RobertDaleSmith/mouthpad-usb/ncs/app/src/ble_nus_client.c

/*
 * Copyright (c) 2025 Robert Dale Smith
 * Copyright (c) 2025 Augmental Tech
 *
 * SPDX-License-Identifier: Apache-2.0
 */

#include "ble_nus_client.h"
#include <zephyr/kernel.h>
#include <zephyr/bluetooth/bluetooth.h>
#include <zephyr/bluetooth/conn.h>
#include <zephyr/bluetooth/uuid.h>
#include <zephyr/bluetooth/gatt.h>
#include <bluetooth/services/nus_client.h>
#include <bluetooth/services/nus.h>
#include <bluetooth/gatt_dm.h>
#include <zephyr/logging/log.h>

LOG_MODULE_REGISTER(ble_nus_client, LOG_LEVEL_INF);

/* NUS Client instance */
static struct bt_nus_client nus_client;

/* Callback functions for external modules */
static ble_nus_data_received_cb_t data_received_cb;
static ble_nus_data_sent_cb_t data_sent_cb;
static ble_nus_mtu_exchange_cb_t mtu_exchange_cb;
static ble_nus_discovery_complete_cb_t discovery_complete_cb;

/* Semaphore for NUS write operations */
K_SEM_DEFINE(nus_write_sem, 0, 1);

/* NUS Client callbacks */
static uint8_t nus_data_received(struct bt_nus_client *nus, const uint8_t *data, uint16_t len);
static void nus_data_sent(struct bt_nus_client *nus, uint8_t err, const uint8_t *const data, uint16_t len);

/* Discovery callbacks */
static void discovery_complete(struct bt_gatt_dm *dm, void *context);
static void discovery_service_not_found(struct bt_conn *conn, void *context);
static void discovery_error(struct bt_conn *conn, int err, void *context);

/* MTU exchange callback */
static void exchange_func(struct bt_conn *conn, uint8_t err, struct bt_gatt_exchange_params *params);

/* Discovery callback structure */
struct bt_gatt_dm_cb discovery_cb = {
	.completed = discovery_complete,
	.service_not_found = discovery_service_not_found,
	.error_found = discovery_error,
};

/* NUS Client callback implementations */
static uint8_t nus_data_received(struct bt_nus_client *nus, const uint8_t *data, uint16_t len)
{
	ARG_UNUSED(nus);

	// Call external data received callback if registered
	if (data_received_cb) {
		data_received_cb(data, len);
	}

	return BT_GATT_ITER_CONTINUE;
}

static void nus_data_sent(struct bt_nus_client *nus, uint8_t err, const uint8_t *const data, uint16_t len)
{
	ARG_UNUSED(nus);
	ARG_UNUSED(data);
	ARG_UNUSED(len);

	k_sem_give(&nus_write_sem);

	if (err) {
		LOG_WRN("ATT error code: 0x%02X", err);
	}

	// Call external data sent callback if registered
	if (data_sent_cb) {
		data_sent_cb(err);
	}
}

/* Discovery callback implementations */
static void discovery_complete(struct bt_gatt_dm *dm, void *context)
{
	struct bt_nus_client *nus = context;
	LOG_INF("Service discovery completed");

	bt_gatt_dm_data_print(dm);

	bt_nus_handles_assign(dm, nus);
	bt_nus_subscribe_receive(nus);

	bt_gatt_dm_data_release(dm);

	// Call external discovery complete callback if registered
	if (discovery_complete_cb) {
		discovery_complete_cb();
	}
}

static void discovery_service_not_found(struct bt_conn *conn, void *context)
{
	LOG_INF("Service not found");
}

static void discovery_error(struct bt_conn *conn, int err, void *context)
{
	LOG_WRN("Error while discovering GATT database: (%d)", err);
}

/* MTU exchange callback implementation */
static void exchange_func(struct bt_conn *conn, uint8_t err, struct bt_gatt_exchange_params *params)
{
	ARG_UNUSED(conn);
	ARG_UNUSED(params);

	if (!err) {
		uint16_t mtu = bt_gatt_get_mtu(conn);
		LOG_INF("MTU EXCHANGE SUCCESSFUL: MTU = %d bytes", mtu);

		// Call external MTU exchange callback if registered
		if (mtu_exchange_cb) {
			mtu_exchange_cb(mtu);
		}
	} else {
		LOG_ERR("MTU EXCHANGE FAILED: error = %d", err);
	}
}

/* Public API implementations */
int ble_nus_client_init(void)
{
	int err;
	struct bt_nus_client_init_param init = {
		.cb = {
			.received = nus_data_received,
			.sent = nus_data_sent,
		}
	};

	err = bt_nus_client_init(&nus_client, &init);
	if (err) {
		LOG_ERR("NUS Client initialization failed (err %d)", err);
		return err;
	}

	LOG_INF("NUS Client module initialized");
	return err;
}

int ble_nus_client_send_data(const uint8_t *data, uint16_t len)
{
	if (!data || len == 0) {
		return -EINVAL;
	}

	return bt_nus_client_send(&nus_client, data, len);
}

void ble_nus_client_discover(struct bt_conn *conn)
{
	int err;

	err = bt_gatt_dm_start(conn,
			       BT_UUID_NUS_SERVICE,
			       &discovery_cb,
			       &nus_client);
	if (err) {
		LOG_ERR("could not start the discovery procedure, error "
			"code: %d", err);
	}
}

void ble_nus_client_register_data_received_cb(ble_nus_data_received_cb_t cb)
{
	data_received_cb = cb;
}

void ble_nus_client_register_data_sent_cb(ble_nus_data_sent_cb_t cb)
{
	data_sent_cb = cb;
}

void ble_nus_client_register_mtu_exchange_cb(ble_nus_mtu_exchange_cb_t cb)
{
	mtu_exchange_cb = cb;
}

void ble_nus_client_register_discovery_complete_cb(ble_nus_discovery_complete_cb_t cb)
{
	discovery_complete_cb = cb;
}

struct bt_nus_client *ble_nus_client_get_instance(void)
{
	return &nus_client;
}

/* Helper function to perform MTU exchange */
int ble_nus_client_exchange_mtu(struct bt_conn *conn)
{
	int err;
	static struct bt_gatt_exchange_params exchange_params;

	exchange_params.func = exchange_func;
	// Request maximum MTU (247 bytes) to handle bigger packets
	err = bt_gatt_exchange_mtu(conn, &exchange_params);
	if (err) {
		LOG_WRN("MTU exchange failed (err %d)", err);
	}

	return err;
}
