RobertDaleSmith/mouthpad-usb/ncs/app/src/ble_transport.h

/*
 * Copyright (c) 2025 Robert Dale Smith
 * Copyright (c) 2025 Augmental Tech
 *
 * SPDX-License-Identifier: Apache-2.0
 */

#ifndef BLE_TRANSPORT_H
#define BLE_TRANSPORT_H

#include <zephyr/kernel.h>
#include <zephyr/bluetooth/conn.h>

/* Callback function types */
typedef void (*ble_data_callback_t)(const uint8_t *data, uint16_t len);
typedef void (*ble_ready_callback_t)(void);

/* BLE Transport initialization and control functions */
int ble_transport_init(void);
int ble_transport_start_bridging(void);

/* USB CDC callback type */
typedef void (*usb_cdc_send_cb_t)(const uint8_t *data, uint16_t len);

/* Transport registration functions */
int ble_transport_register_usb_cdc_callback(usb_cdc_send_cb_t cb);
int ble_transport_register_usb_hid_callback(ble_data_callback_t cb);

/* NUS Transport functions */
int ble_transport_send_nus_data(const uint8_t *data, uint16_t len);
bool ble_transport_is_nus_ready(void);

/* Connection status */
bool ble_transport_is_connected(void);
bool ble_transport_has_data_activity(void);
bool ble_transport_has_hid_data_activity(void);
void ble_transport_mark_hid_data_activity(void);
int8_t ble_transport_get_rssi(void);
void ble_transport_set_rssi(int8_t rssi);

/* Device name functions */
void ble_transport_set_device_name(const char *name);
const char *ble_transport_get_device_name(void);

/* Connection control */
void ble_transport_disconnect(void);
void ble_transport_clear_bonds(void);

/* Future HID Transport functions (for later integration) */
int ble_transport_register_hid_data_callback(ble_data_callback_t cb);
int ble_transport_register_hid_ready_callback(ble_ready_callback_t cb);
int ble_transport_send_hid_data(const uint8_t *data, uint16_t len);
bool ble_transport_is_hid_ready(void);

/* Internal transport state management */
void ble_transport_handle_connection(struct bt_conn *conn);
void ble_transport_handle_disconnection(struct bt_conn *conn, uint8_t reason);

#endif /* BLE_TRANSPORT_H */
