RobertDaleSmith/mouthpad-usb/ncs/app/src/oled_display.h

/*
 * Copyright (c) 2025 Robert Dale Smith
 * Copyright (c) 2025 Augmental Tech
 *
 * SPDX-License-Identifier: Apache-2.0
 */

#ifndef OLED_DISPLAY_H_
#define OLED_DISPLAY_H_

#include <stdint.h>
#include <stdbool.h>

#ifdef __cplusplus
extern "C" {
#endif

/**
 * @brief Initialize the OLED display
 * 
 * @return 0 on success, negative error code on failure
 */
int oled_display_init(void);

/**
 * @brief Clear the entire display
 * 
 * @return 0 on success, negative error code on failure
 */
int oled_display_clear(void);

/**
 * @brief Update the display with current battery level, connection status, and signal strength
 * 
 * @param battery_level Battery percentage (0-100), or 0xFF if unknown
 * @param is_connected Whether BLE device is connected
 * @param rssi_dbm BLE signal strength in dBm (-128 to 127), or 0 if unknown/not connected
 * @return 0 on success, negative error code on failure
 */
int oled_display_update_status(uint8_t battery_level, bool is_connected, int8_t rssi_dbm);

/**
 * @brief Display a simple message on the OLED
 * 
 * @param message Message to display (null-terminated string)
 * @return 0 on success, negative error code on failure
 */
int oled_display_message(const char *message);

/**
 * @brief Display device information screen
 * 
 * @param device_name Connected device name (or "Not Connected")
 * @param connection_count Number of successful connections since boot
 * @return 0 on success, negative error code on failure
 */
int oled_display_device_info(const char *device_name, uint32_t connection_count);

/**
 * @brief Check if OLED display is available and ready for use
 * 
 * @return true if display is available, false otherwise
 */
bool oled_display_is_available(void);

/**
 * @brief Display splash screen with Augmental logo
 * 
 * @param duration_ms How long to show splash screen (0 = show until next update)
 * @return 0 on success, negative error code on failure
 */
int oled_display_splash_screen(uint32_t duration_ms);

/**
 * @brief Reset display state to force next status update
 * 
 * Call this to ensure the next oled_display_update_status() will update
 * regardless of current values
 */
void oled_display_reset_state(void);

/**
 * @brief Display scanning status
 * 
 * Shows "Scanning..." message on display
 * @return 0 on success, negative error code on failure
 */
int oled_display_scanning(void);

/**
 * @brief Display device found status
 * 
 * Shows "Device Found" and device name if provided
 * @param device_name Name of found device (optional, can be NULL)
 * @return 0 on success, negative error code on failure
 */
int oled_display_device_found(const char *device_name);

/**
 * @brief Display pairing status
 * 
 * Shows "Pairing..." message on display
 * @return 0 on success, negative error code on failure
 */
int oled_display_pairing(void);

#ifdef __cplusplus
}
#endif

#endif /* OLED_DISPLAY_H_ */
